omerkarslioglu/forward_converter_pi_control/SOFT/Core/Src/ADC_READ.c

/* ADC READ .c FILE FOR STM32F407VG */

/* BY OMER KARSLIOGLU */
#include "ADC_READ.h"


void ADC_Select_CH0(void)
{
    ADC_ChannelConfTypeDef sConfig = {0};
	sConfig.Channel = ADC_CHANNEL_0;
	sConfig.Rank = 1;
	sConfig.SamplingTime = ADC_SAMPLETIME_84CYCLES;
	if (HAL_ADC_ConfigChannel(&hadc1, &sConfig) != HAL_OK)
	{
		Error_Handler();
	}
}

void ADC_Select_CH1(void)
{
	ADC_ChannelConfTypeDef sConfig = {0};
	sConfig.Channel = ADC_CHANNEL_1;
	sConfig.Rank = 1;
	sConfig.SamplingTime = ADC_SAMPLETIME_28CYCLES;
	if (HAL_ADC_ConfigChannel(&hadc1, &sConfig) != HAL_OK)
	{
		Error_Handler();
	}
}

void ADC_Select_CH2(void)
{
	ADC_ChannelConfTypeDef sConfig = {0};
	sConfig.Channel = ADC_CHANNEL_2;
	sConfig.Rank = 1;
	sConfig.SamplingTime = ADC_SAMPLETIME_28CYCLES;
	if (HAL_ADC_ConfigChannel(&hadc1, &sConfig) != HAL_OK)
	{
		Error_Handler();
	}
}
